marydovika/AWS/CAD MODELS__Ver3/Picture1.jpg

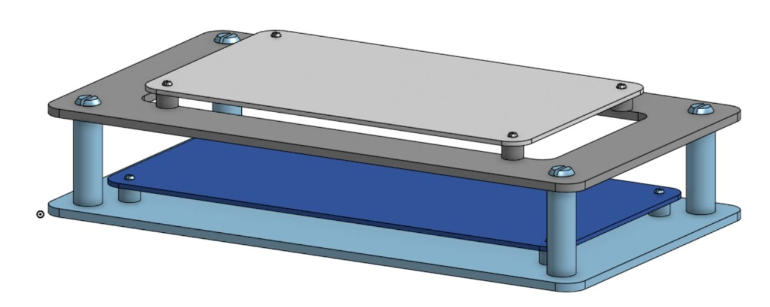
CAD MODELS__Ver3/Picture1.jpg
