marydovika/AWS/IMAGES__Ver1/CASE DESIGN/design 1/Screenshot 2026-01-07 221652.png

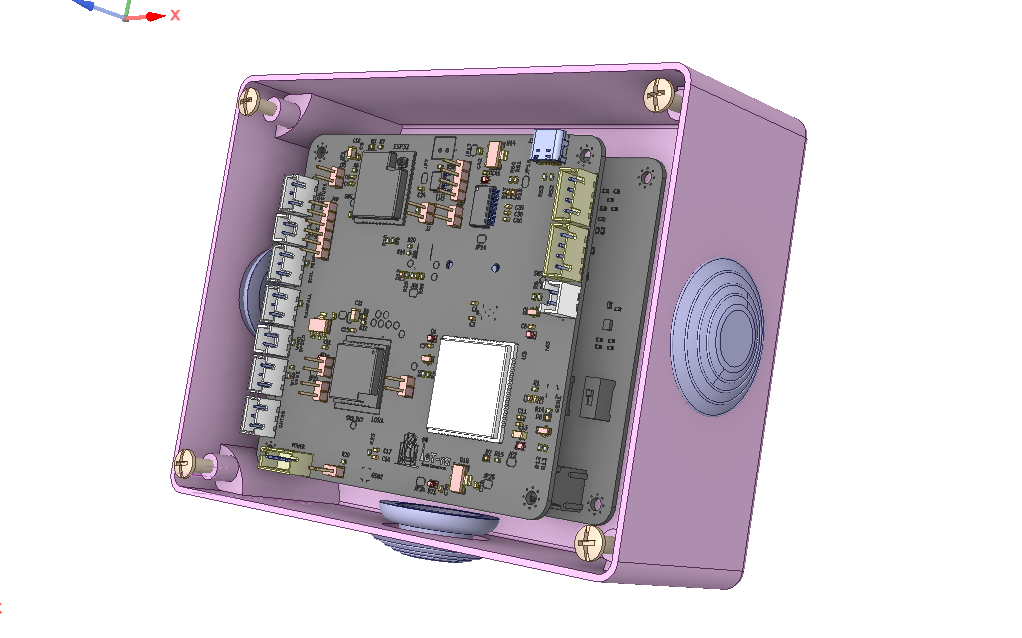
IMAGES__Ver1/CASE DESIGN/design 1/Screenshot 2026-01-07 221652.png
