marydovika/AWS/IMAGES__Ver1/CASE DESIGN/design 1/Screenshot 2026-01-07 221702.png

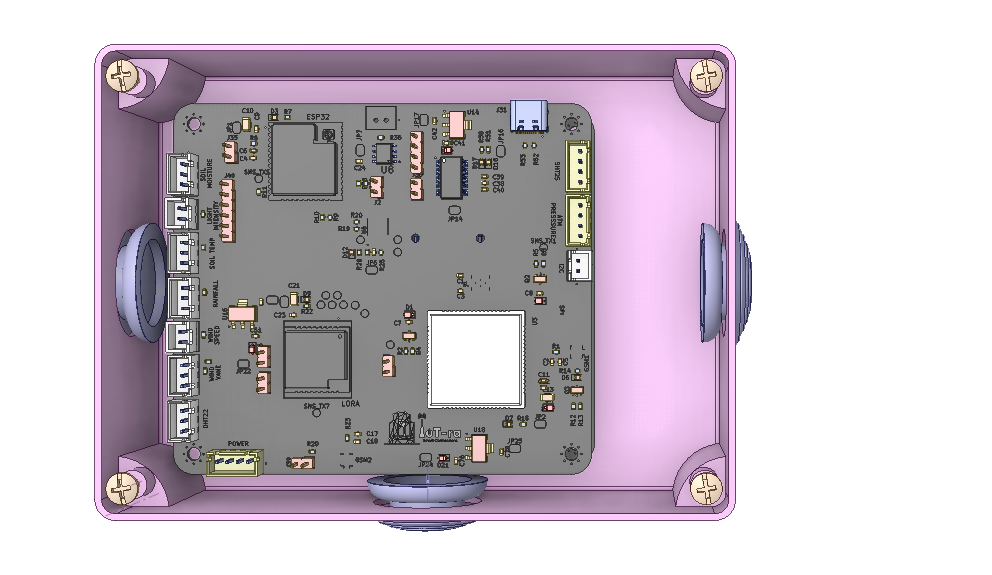
IMAGES__Ver1/CASE DESIGN/design 1/Screenshot 2026-01-07 221702.png
