marydovika/AWS/IMAGES__Ver1/CASE DESIGN/design 2/Screenshot 2026-01-08 164800.png

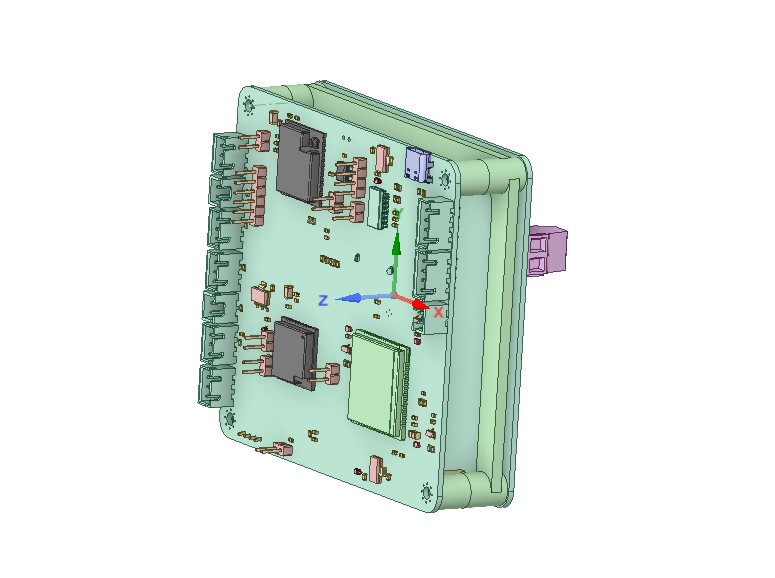
IMAGES__Ver1/CASE DESIGN/design 2/Screenshot 2026-01-08 164800.png
