marydovika/AWS/IMAGES__Ver1/CASE DESIGN/design 2/Screenshot 2026-01-08 214220.png

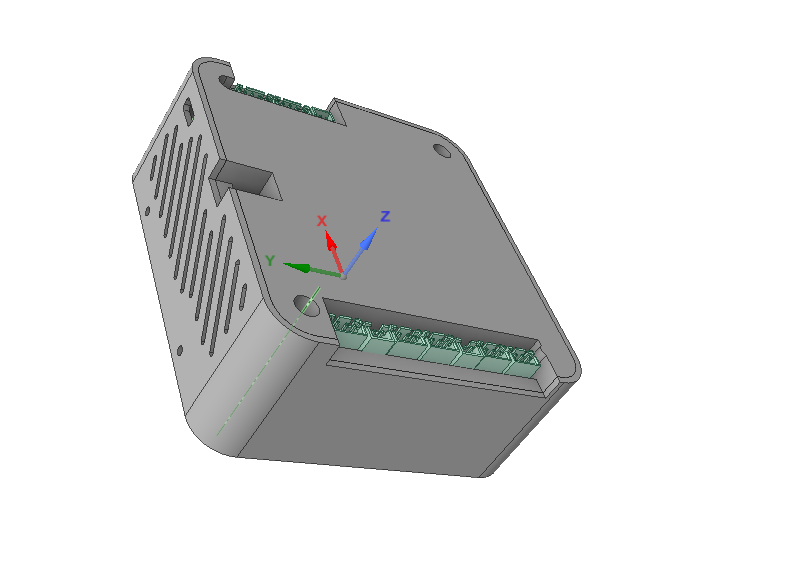
IMAGES__Ver1/CASE DESIGN/design 2/Screenshot 2026-01-08 214220.png
