marydovika/AWS/IMAGES__Ver1/GATEWAY BOARD images/Current design/BACK GREEN.png

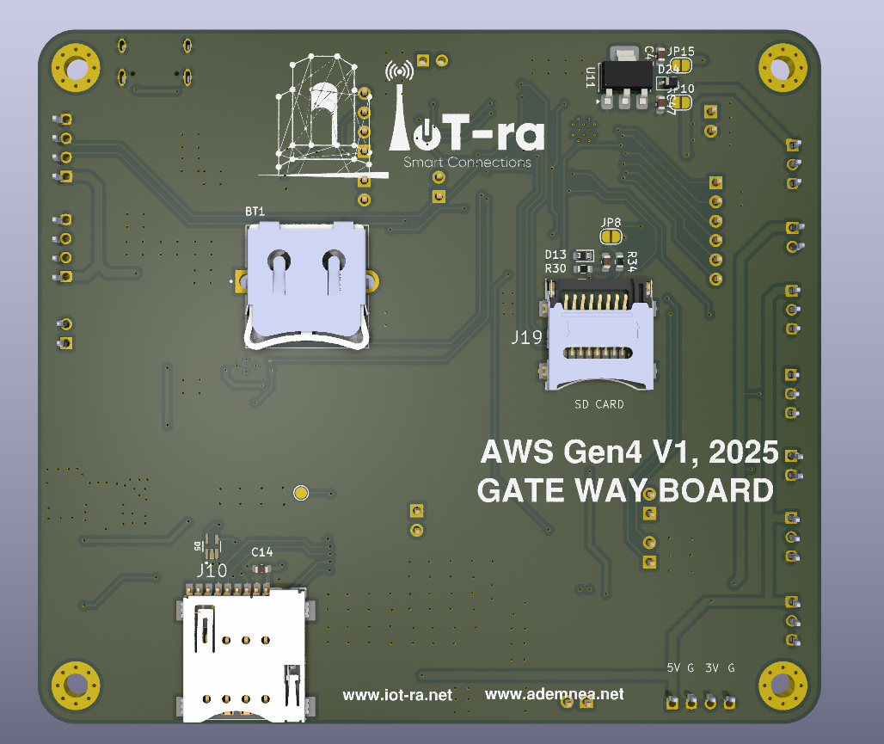
IMAGES__Ver1/GATEWAY BOARD images/Current design/BACK GREEN.png
