marydovika/AWS/IMAGES__Ver1/GATEWAY BOARD images/Current design/FRONT GREEN.png

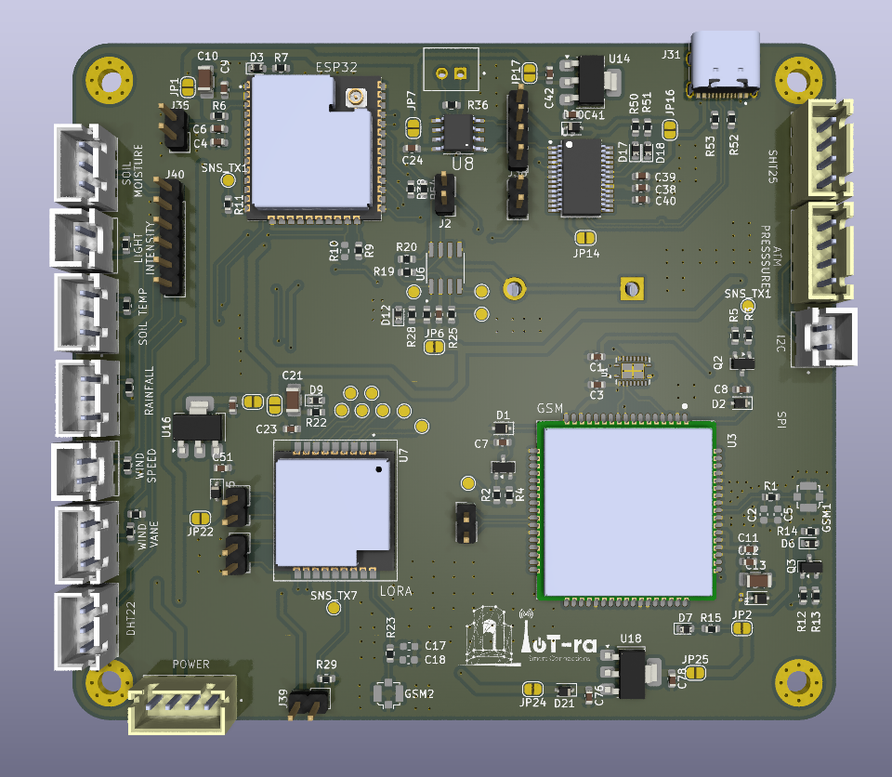
IMAGES__Ver1/GATEWAY BOARD images/Current design/FRONT GREEN.png
