marydovika/AWS/IMAGES__Ver1/POWER BOARD images/Current design/FRONT GREEN.png

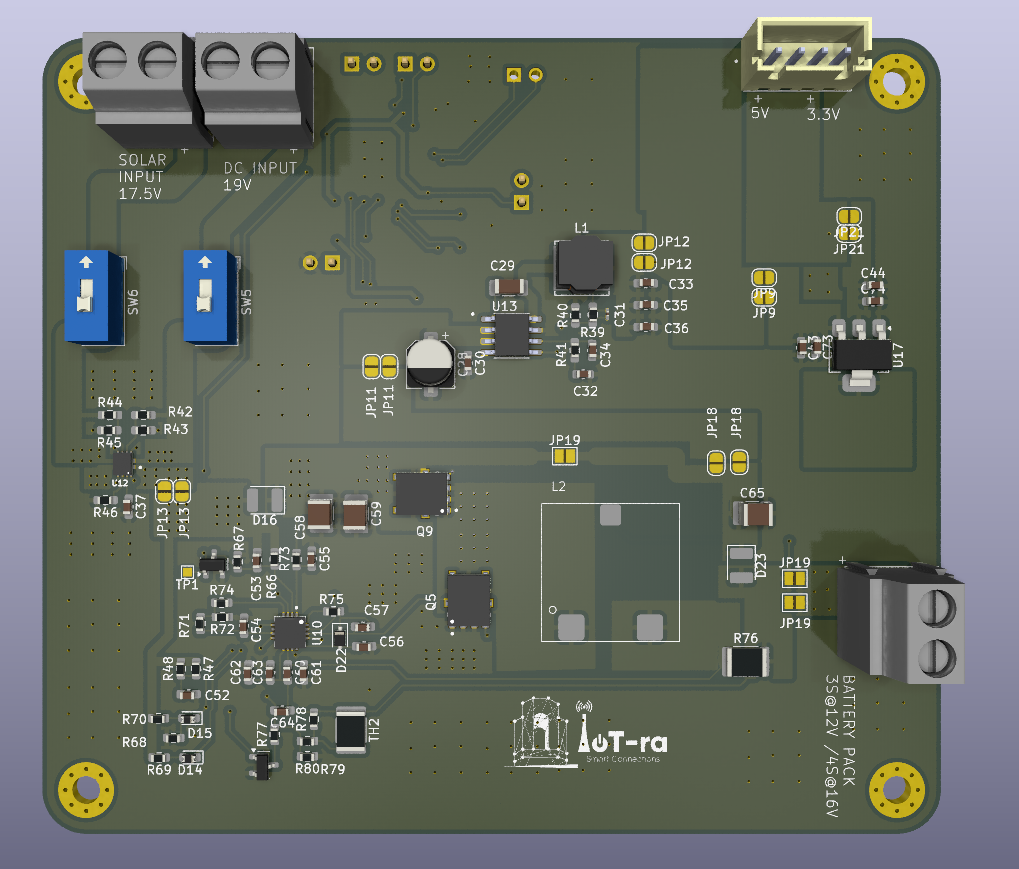
IMAGES__Ver1/POWER BOARD images/Current design/FRONT GREEN.png
