marydovika/AWS/PROJECT CODE/version one/include/GSM.h

#ifndef GSM_H
#define GSM_H

#include <Arduino.h>

class GSM {
public:
    GSM();
    void setupGSM();
    void connectGPRS(); // New: Setup Internet
    // Sends data to a specific ThingSpeak URL
    void sendThingSpeakRequest(String url); 

private:
    void sendCommand(const String& command, int timeout, boolean debug);
};

#endif
